bk1285/rpi_wordclock/wordclock_layouts/dutch_10x9/stancil_front.png

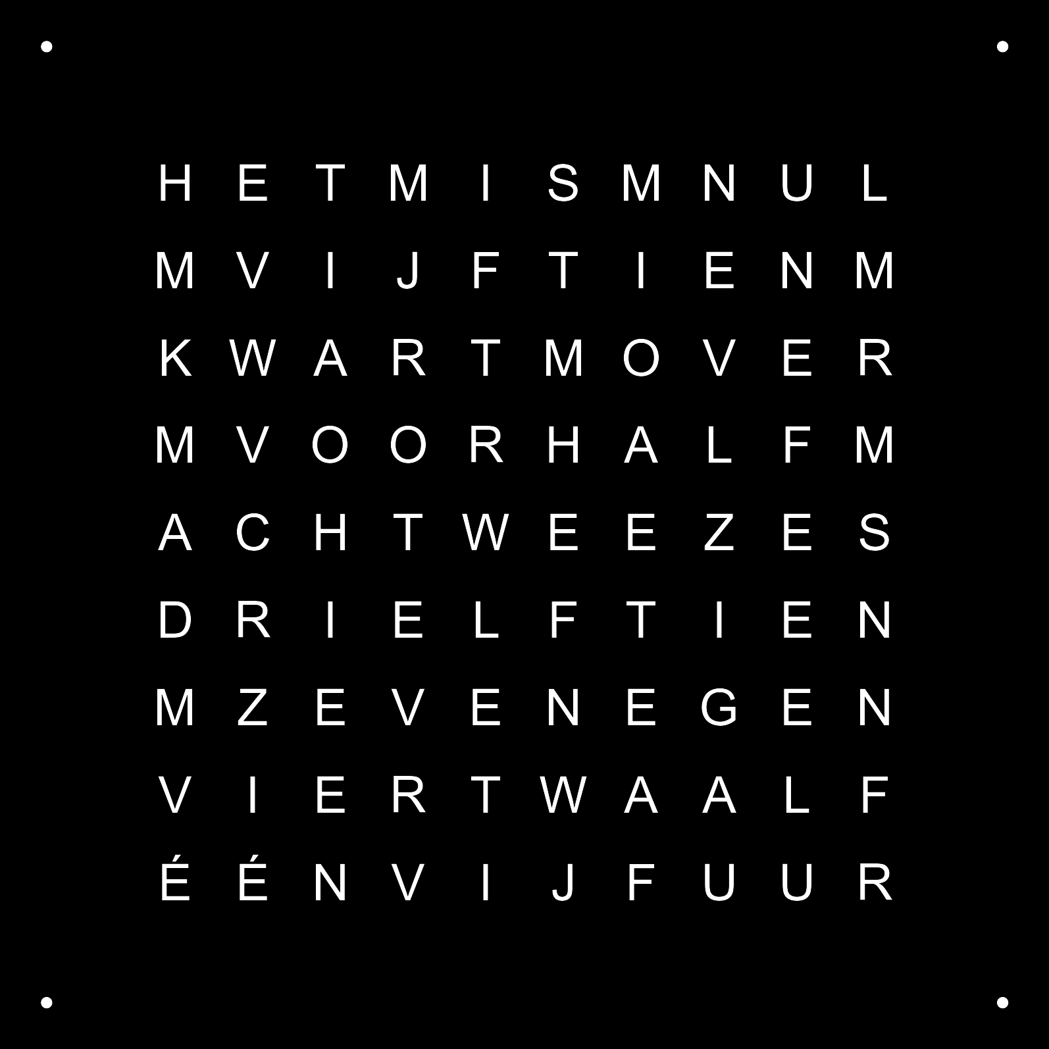
wordclock_layouts/dutch_10x9/stancil_front.png
