bk1285/rpi_wordclock/wordclock_layouts/dutch_11x10/stencil_front.png

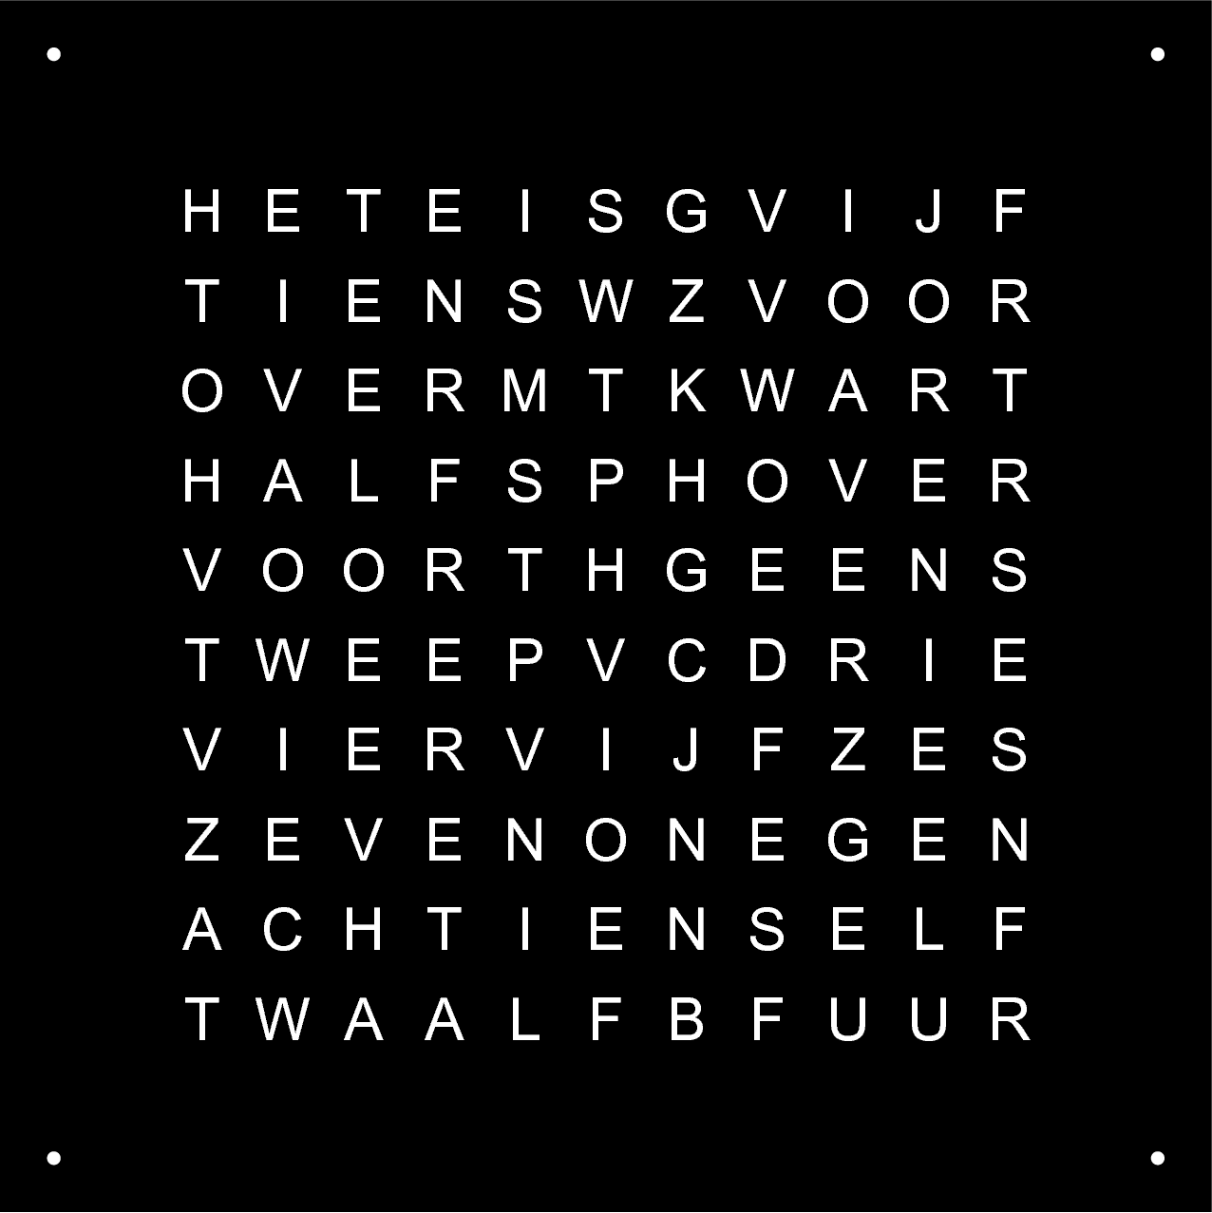
wordclock_layouts/dutch_11x10/stencil_front.png
