bk1285/rpi_wordclock/wordclock_layouts/english_11x10/stancil_front.png

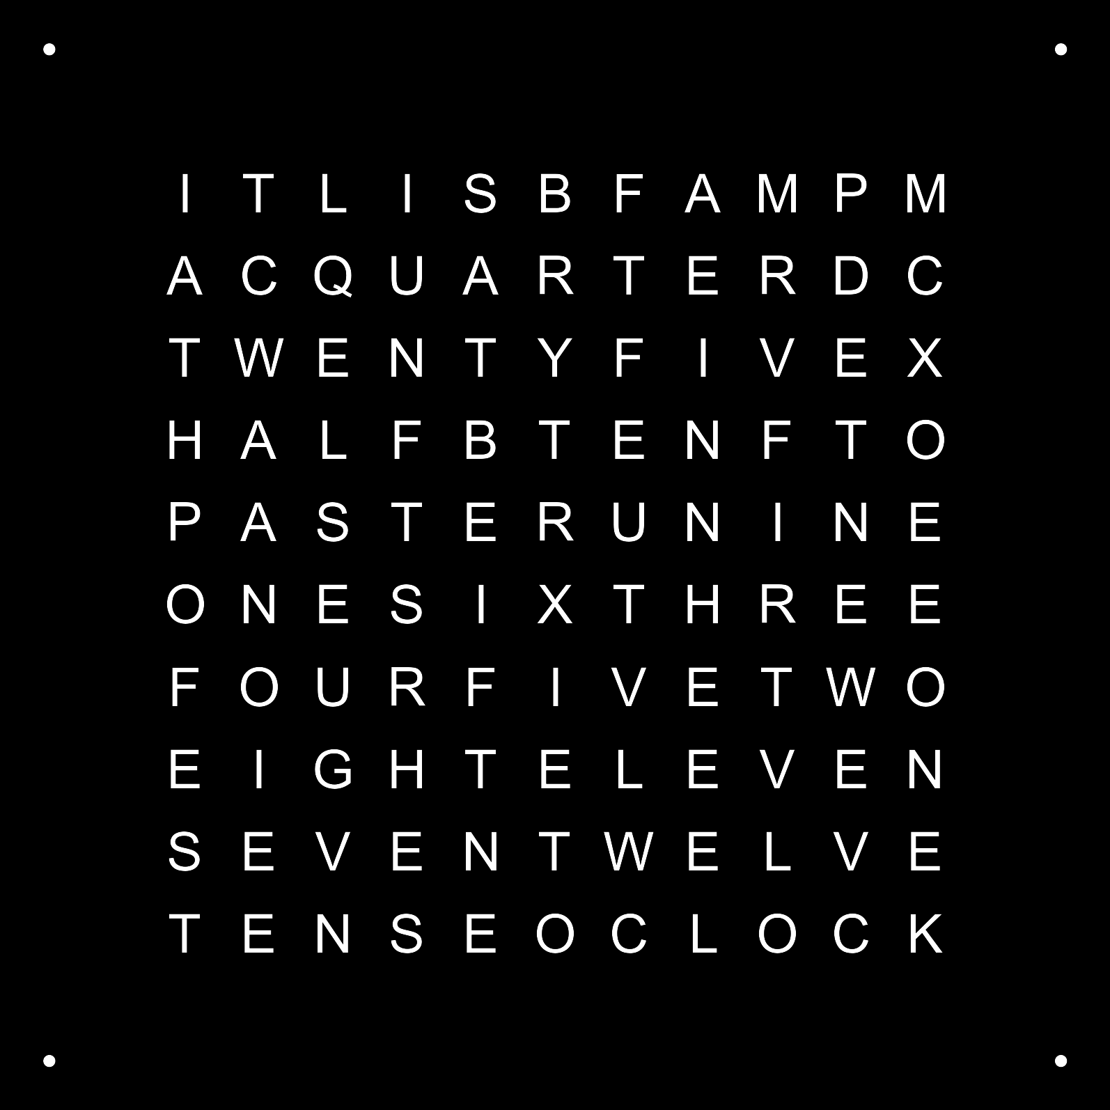
wordclock_layouts/english_11x10/stancil_front.png
