bk1285/rpi_wordclock/wordclock_layouts/french_11x10/stancil_front.png

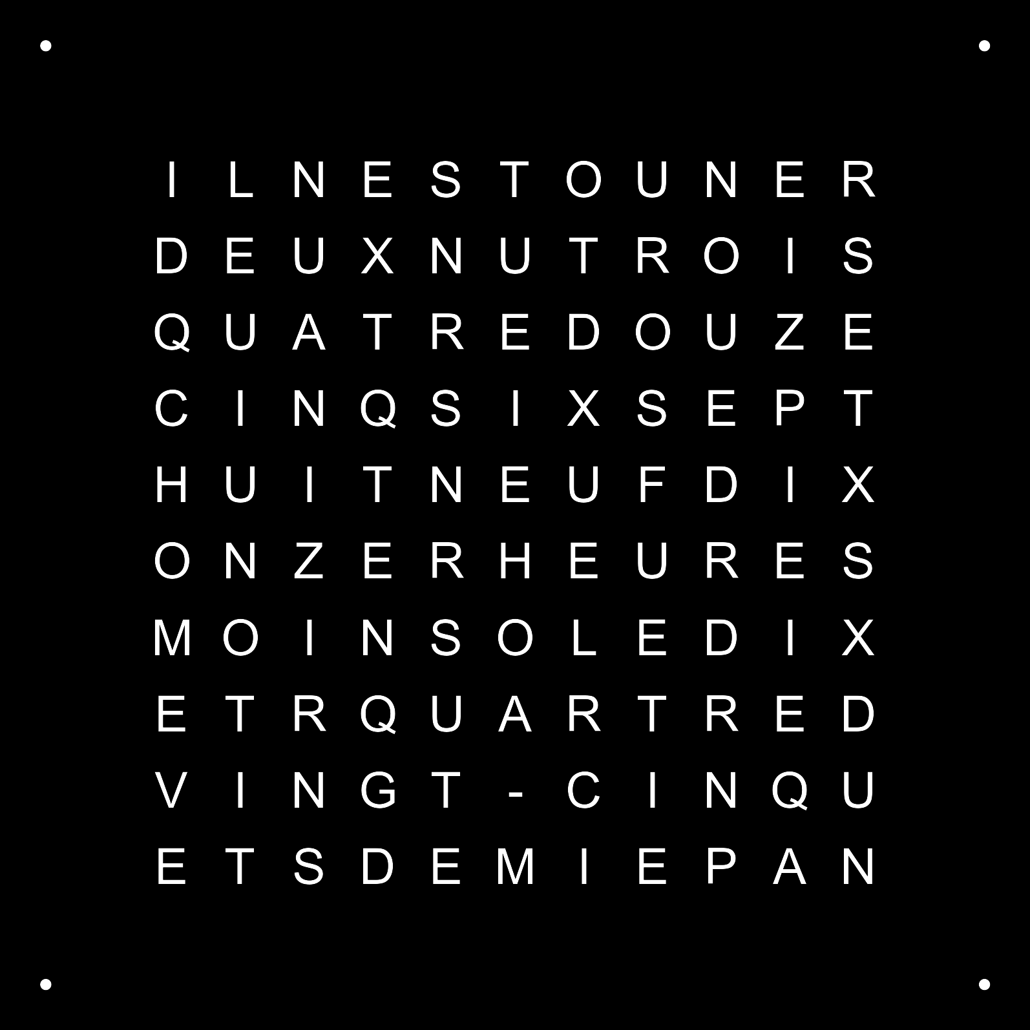
wordclock_layouts/french_11x10/stancil_front.png
