bk1285/rpi_wordclock/wordclock_layouts/romanian_11x10/stencil_front_.png

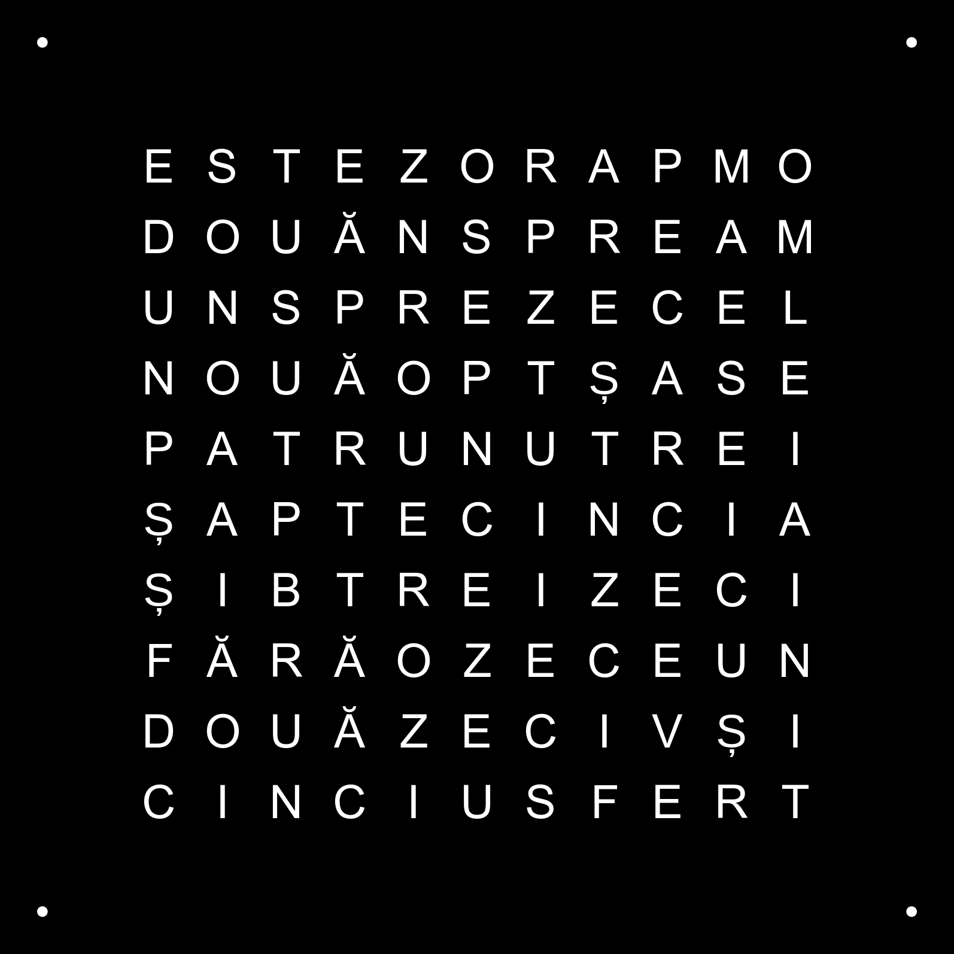
wordclock_layouts/romanian_11x10/stencil_front_.png
