bk1285/rpi_wordclock/wordclock_layouts/turkish_11x10/stancil_front.png

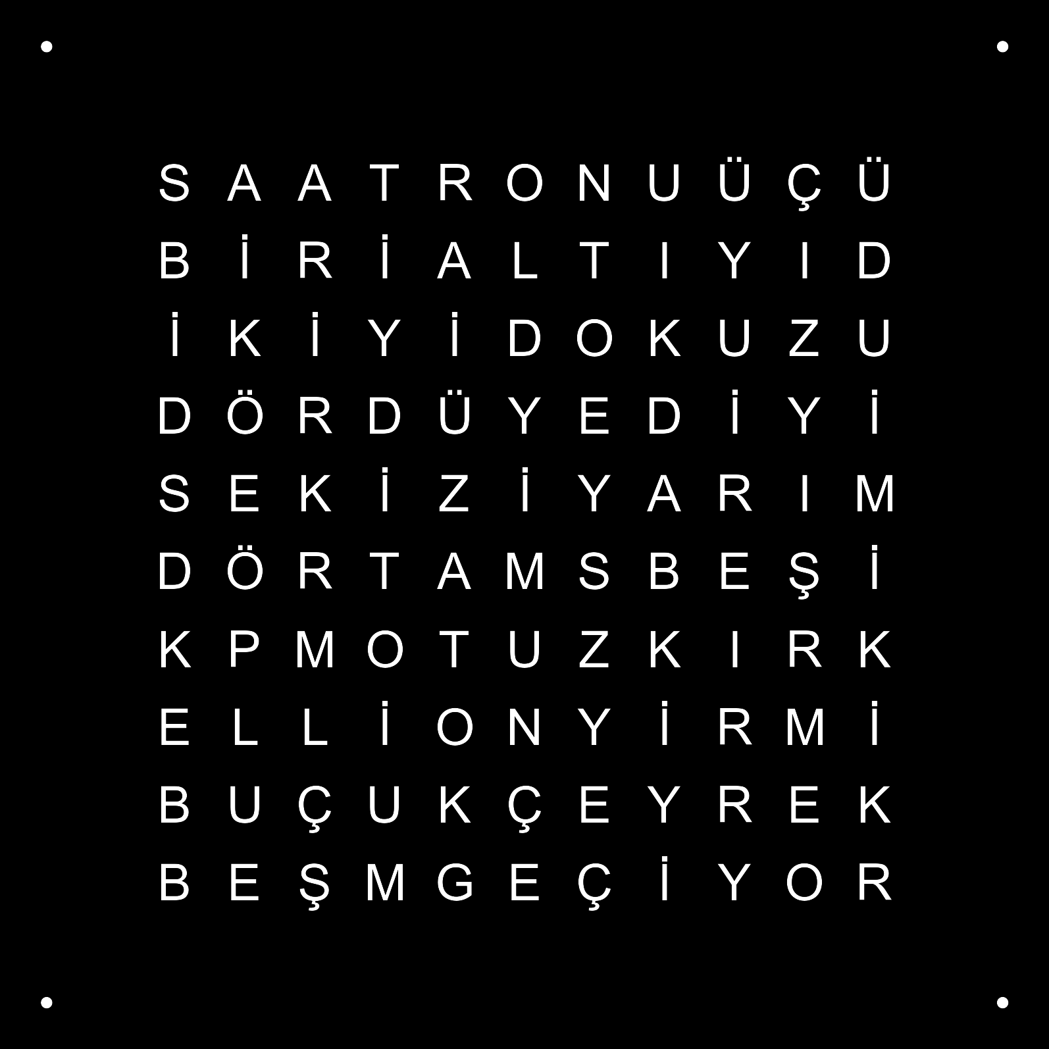
wordclock_layouts/turkish_11x10/stancil_front.png
