bk1285/rpi_wordclock/wordclock_tools/wordclock_strip_neopixel.py

from rpi_ws281x import Adafruit_NeoPixel, ws
from rpi_ws281x import Color as NeoPixelColor
import wordclock_tools.wordclock_colors as wcc
import logging

class wordclock_strip_neopixel(Adafruit_NeoPixel):

    def __init__(self, wcl):
        try:
            super(wordclock_strip_neopixel, self).__init__(wcl.LED_COUNT, wcl.LED_PIN, wcl.LED_FREQ_HZ,
                                                wcl.LED_DMA, wcl.LED_INVERT, 255 , 0, ws.WS2811_STRIP_GRB)
        except:
            logging.error('Update deprecated external dependency rpi_ws281x. '
                    'For details see also https://github.com/jgarff/rpi_ws281x/blob/master/python/README.md')

    def setPixelColor(self, index, color):
        """
        Here we receive a wordclock color as input and convert it to a NeoPixelColor.
        """
        neopixelcolor = NeoPixelColor(color.r, color.g, color.b)
        super(wordclock_strip_neopixel, self).setPixelColor(index, neopixelcolor)
