bk1285/rpi_wordclock/wordclock_tools/wordclock_screen.py

import wordclock_tools.wordclock_colors as wcc
import logging

class wordclock_screen:

    def __init__(self, wcd):
        self.matrix = [[wcc.BLACK for _ in range(wcd.get_wca_height())] for _ in
                                      range(wcd.get_wca_width())]

        size = wcd.get_wca_height() * wcd.get_wca_width()
        rest = wcd.get_led_count() - size

        self.minutes = [wcc.BLACK for _ in range(4)]
        if rest >= 4: # subtract minutes
            rest -= 4

        self.misc = [wcc.BLACK for _ in range(rest)]


    def __sub__(self, other):
        if not isinstance(other, int):
            raise TypeError

        self.minutes = [x - other for x in self.minutes]
        self.misc    = [x - other for x in self.misc]
        self.matrix  = [[x - other for x in y] for y in self.matrix]
        return self
